RaihanKP10/FLOPRO-Flood-Prevention-and-River-Observation/Desain UI UX/Pembuatan Desain/Main Dashboard_FLOPRO.jpeg

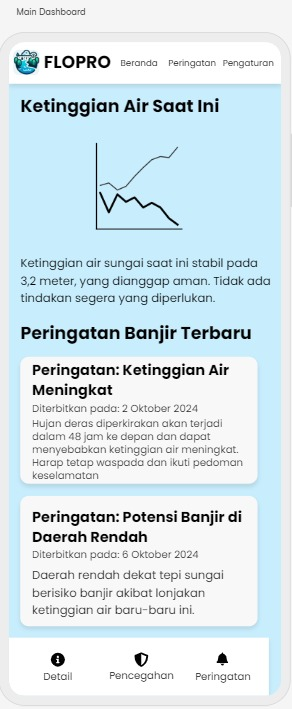
Desain UI UX/Pembuatan Desain/Main Dashboard_FLOPRO.jpeg
