RaihanKP10/FLOPRO-Flood-Prevention-and-River-Observation/Desain UI UX/Pembuatan Desain/User Login Screen_FLOPRO.jpeg

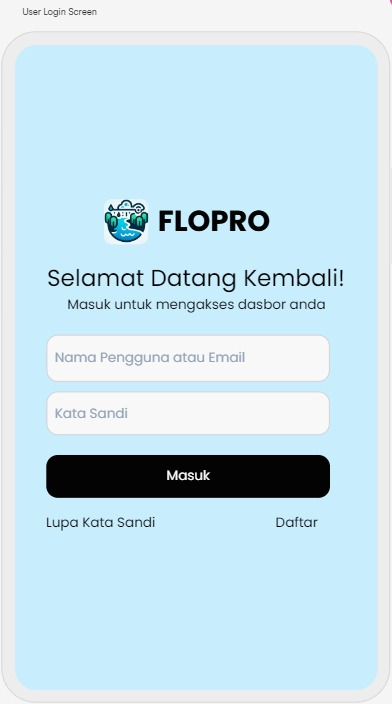
Desain UI UX/Pembuatan Desain/User Login Screen_FLOPRO.jpeg
