RaihanKP10/FLOPRO-Flood-Prevention-and-River-Observation/Desain UI UX/Pembuatan Desain/Water Level Details_FLOPRO.jpeg

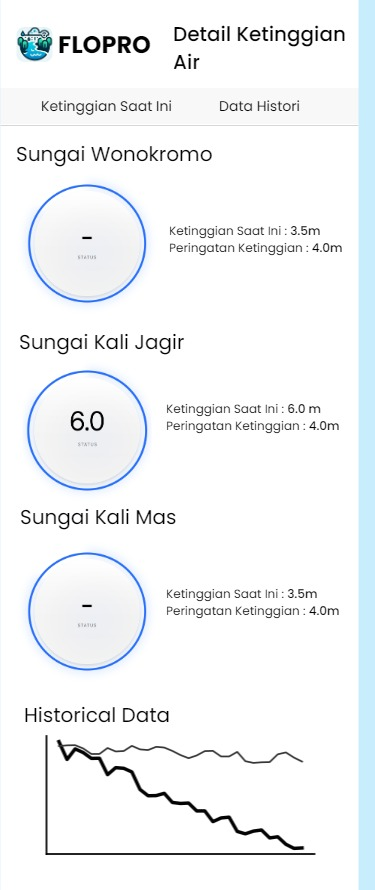
Desain UI UX/Pembuatan Desain/Water Level Details_FLOPRO.jpeg
