RaihanKP10/FLOPRO-Flood-Prevention-and-River-Observation/Desain UI UX/Pembuatan Desain/Welcome Screen_FLOPRO.jpeg

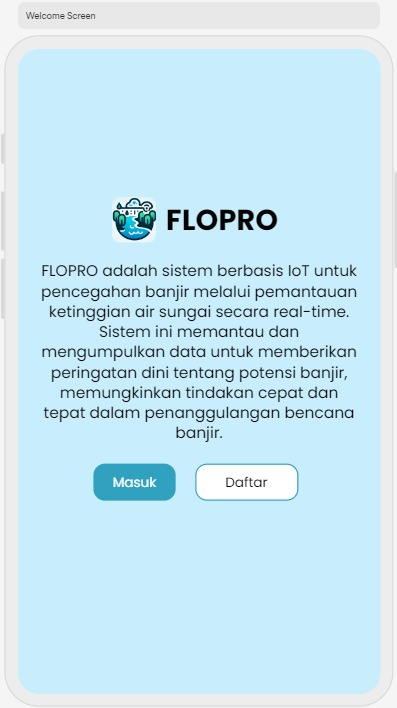
Desain UI UX/Pembuatan Desain/Welcome Screen_FLOPRO.jpeg
