RaihanKP10/FLOPRO-Flood-Prevention-and-River-Observation/Desain UI UX/Sketsa/Main Dashboard_Sketch.jpeg

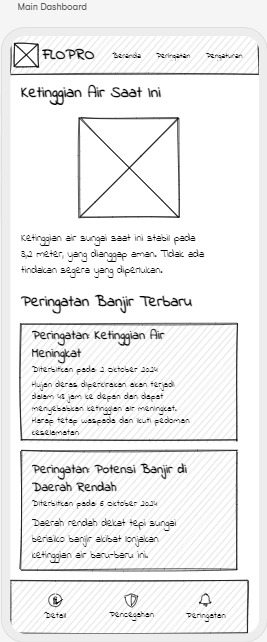
Desain UI UX/Sketsa/Main Dashboard_Sketch.jpeg
