RaihanKP10/FLOPRO-Flood-Prevention-and-River-Observation/Desain UI UX/Sketsa/User Login_Sketch.jpeg

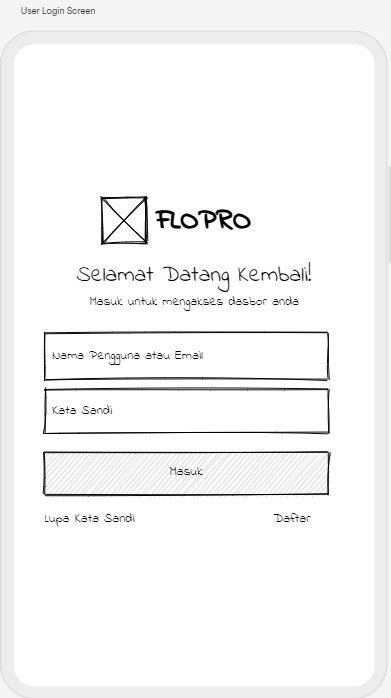
Desain UI UX/Sketsa/User Login_Sketch.jpeg
