RaihanKP10/FLOPRO-Flood-Prevention-and-River-Observation/Desain UI UX/Sketsa/Water Level Details_Sketch.png

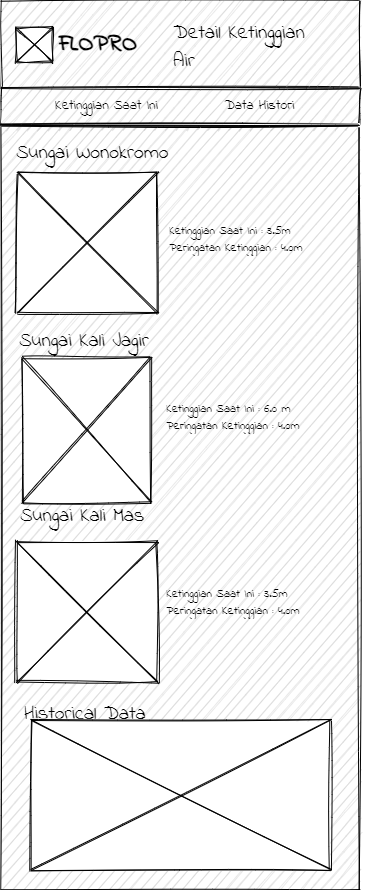
Desain UI UX/Sketsa/Water Level Details_Sketch.png
