RaihanKP10/FLOPRO-Flood-Prevention-and-River-Observation/Desain UI UX/Sketsa/Welcome Screen_Sketch.jpeg

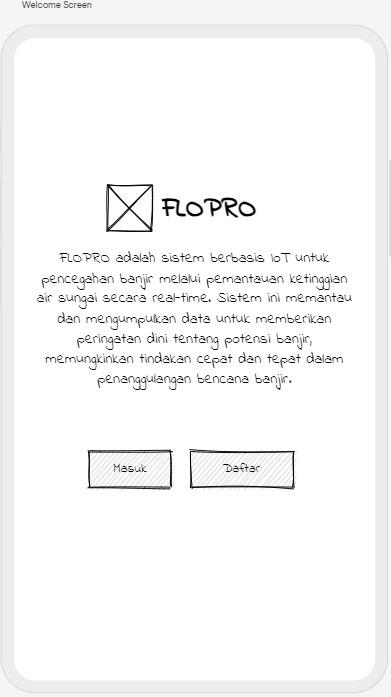
Desain UI UX/Sketsa/Welcome Screen_Sketch.jpeg
