RaihanKP10/FLOPRO-Flood-Prevention-and-River-Observation/Konfigurasi MQTT/Flowchart MQTTT Flopro.jpeg

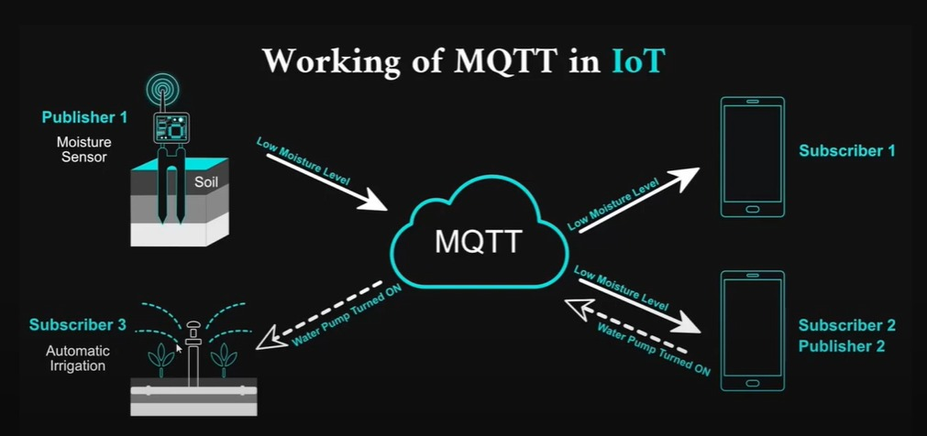
Konfigurasi MQTT/Flowchart MQTTT Flopro.jpeg
