RaihanKP10/FLOPRO-Flood-Prevention-and-River-Observation/Konfigurasi MQTT/Progress 1/Broker Sudah Connect.jpeg

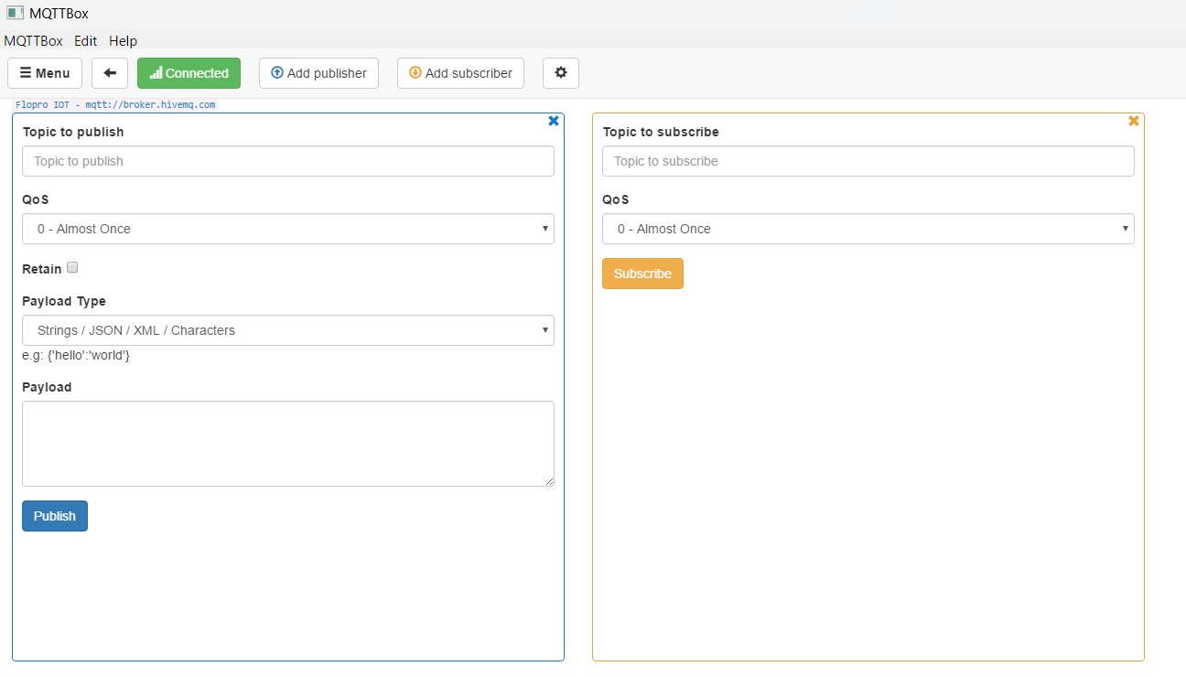
Konfigurasi MQTT/Progress 1/Broker Sudah Connect.jpeg
