RaihanKP10/FLOPRO-Flood-Prevention-and-River-Observation/Konfigurasi MQTT/Progress 1/Daftar HiveMQ.jpeg

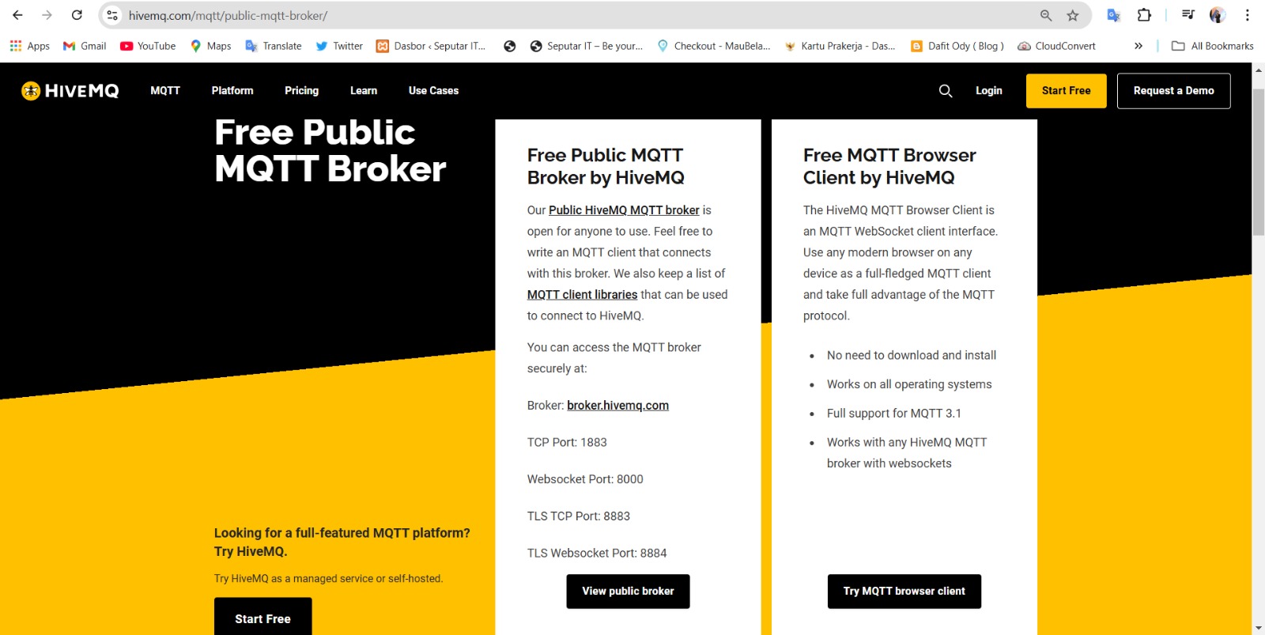
Konfigurasi MQTT/Progress 1/Daftar HiveMQ.jpeg
