RaihanKP10/FLOPRO-Flood-Prevention-and-River-Observation/Konfigurasi MQTT/Progress 1/Menyiapkan Broker Publik (HiveMQ).jpeg

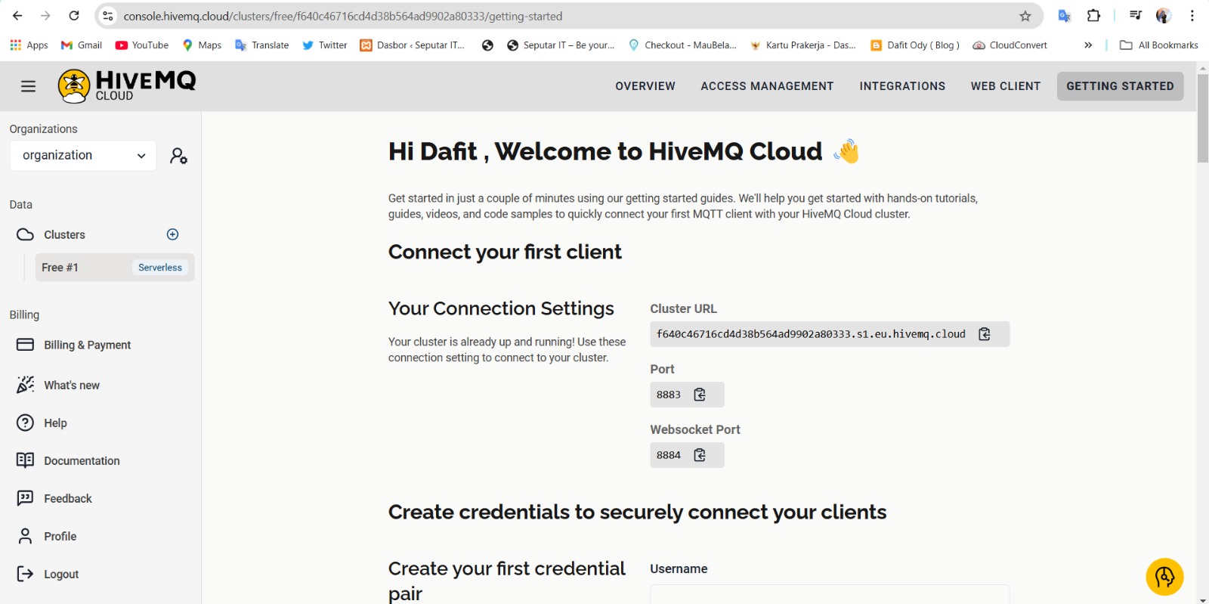
Konfigurasi MQTT/Progress 1/Menyiapkan Broker Publik (HiveMQ).jpeg
