RaihanKP10/FLOPRO-Flood-Prevention-and-River-Observation/Konfigurasi MQTT/Progress 1/Pembuatan MQTT Client.jpeg

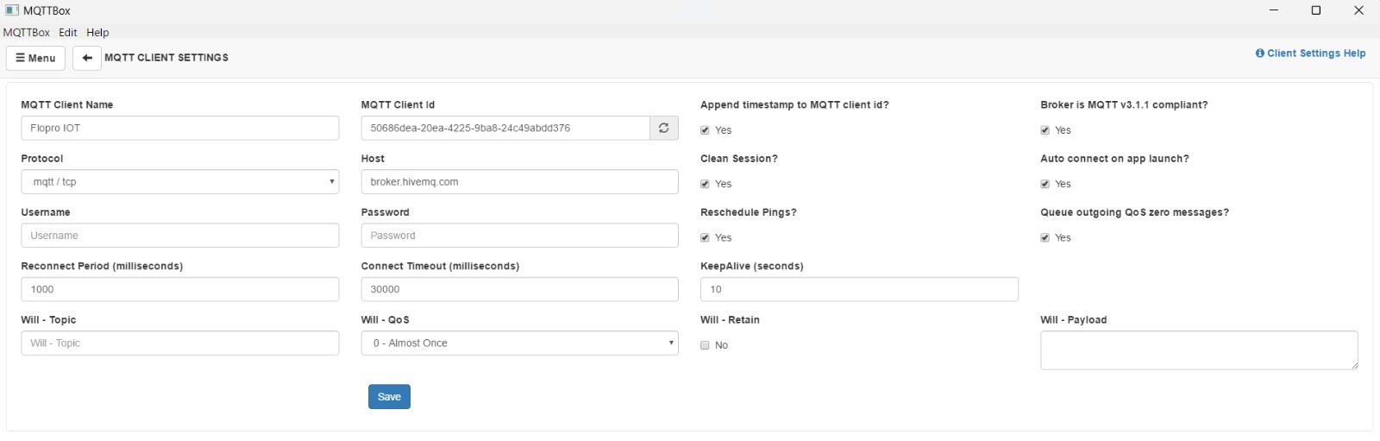
Konfigurasi MQTT/Progress 1/Pembuatan MQTT Client.jpeg
