RaihanKP10/FLOPRO-Flood-Prevention-and-River-Observation/Konfigurasi MQTT/Progress 1/Unduh MQTT Box.png

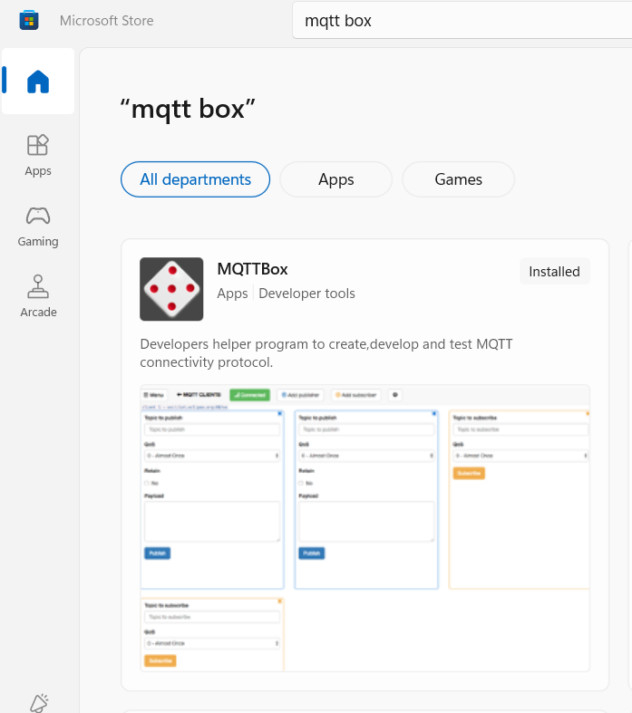
Konfigurasi MQTT/Progress 1/Unduh MQTT Box.png
