RaihanKP10/FLOPRO-Flood-Prevention-and-River-Observation/Pembuatan Aplikasi/Progress 2/Dashboard.jpeg

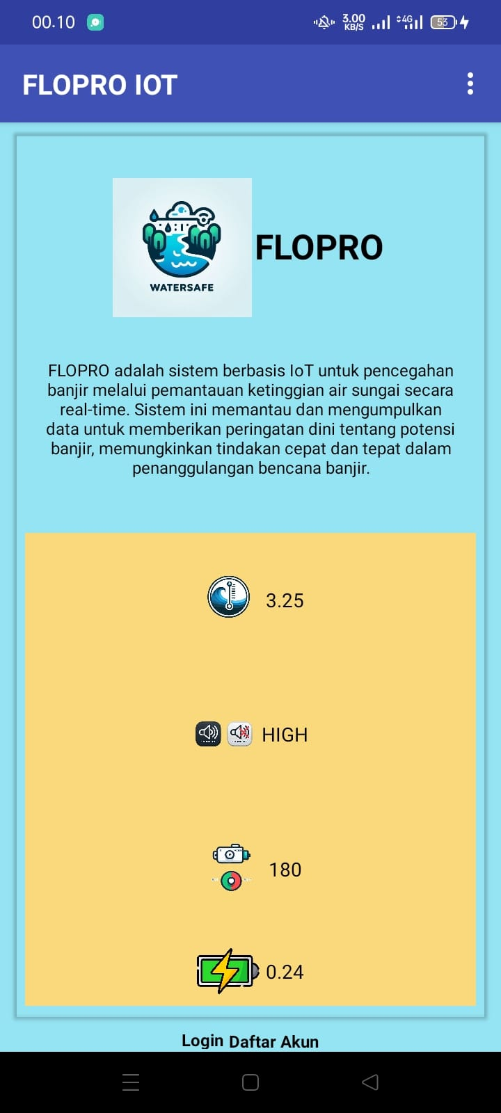
Pembuatan Aplikasi/Progress 2/Dashboard.jpeg
