RaihanKP10/FLOPRO-Flood-Prevention-and-River-Observation/Pembuatan Aplikasi/Progress 2/Pembuatan Daftar Akun.jpeg

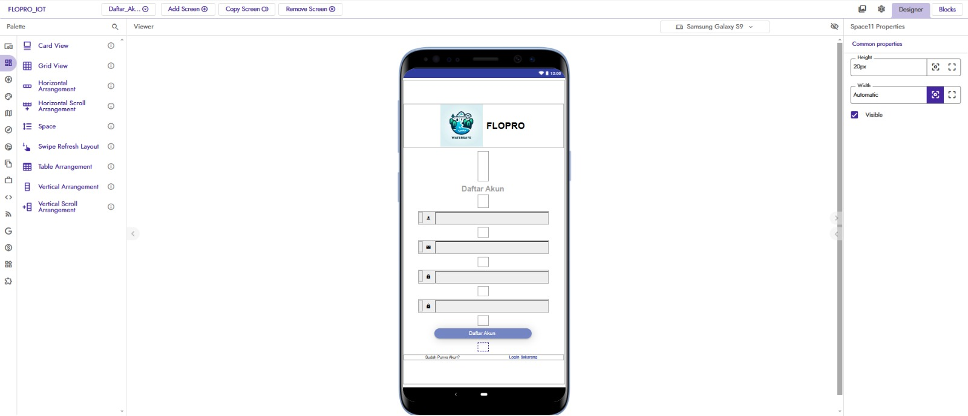
Pembuatan Aplikasi/Progress 2/Pembuatan Daftar Akun.jpeg
