RaihanKP10/FLOPRO-Flood-Prevention-and-River-Observation/Pembuatan Aplikasi/Progress 2/Pembuatan Dashboard.jpeg

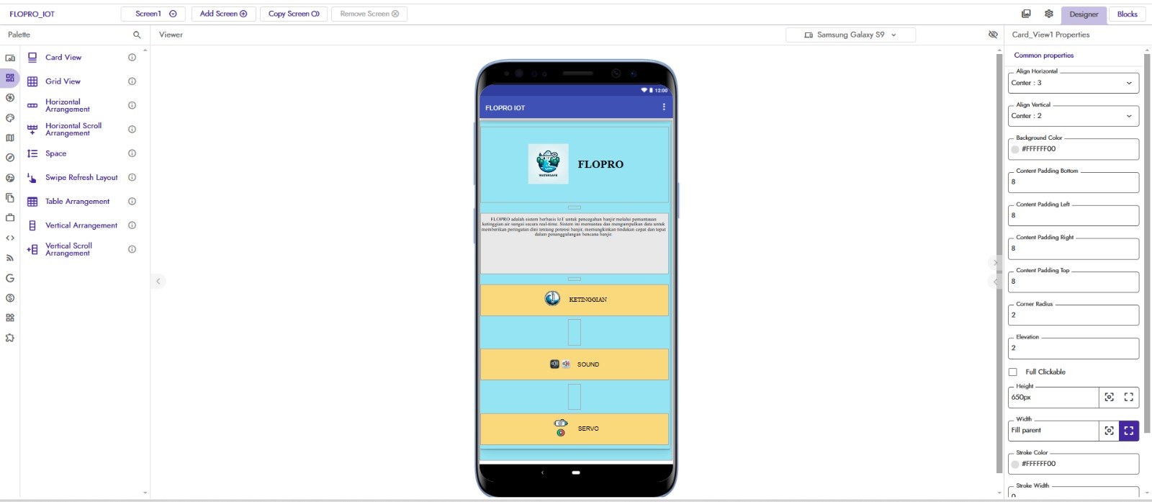
Pembuatan Aplikasi/Progress 2/Pembuatan Dashboard.jpeg
